pixyfrog/oyster-wind-station/oyster-chassis/renders/antenna.png

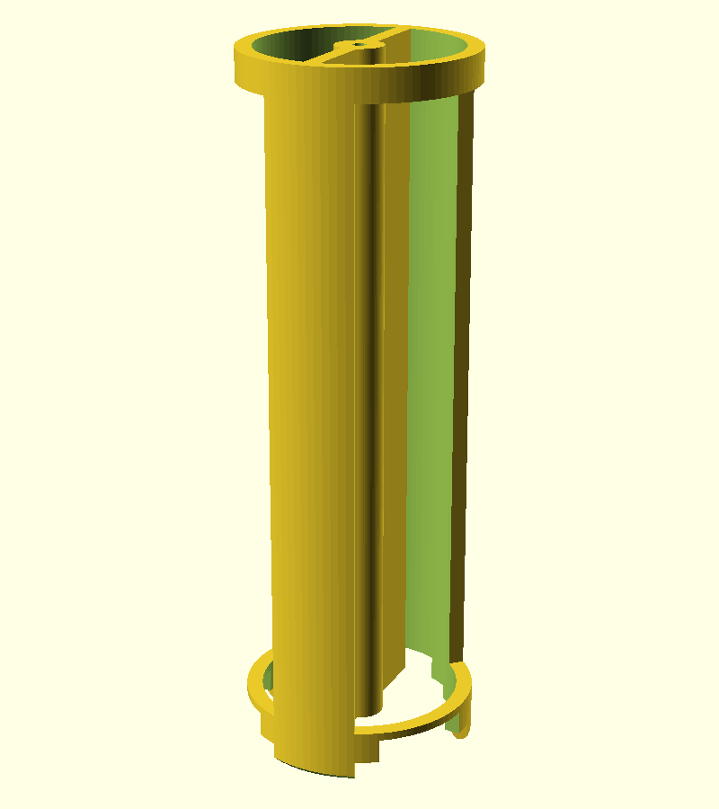
oyster-chassis/renders/antenna.png
