pixyfrog/oyster-wind-station/src/packet.rs

pub fn crc8(data: &[u8]) -> u8 {
    let mut crc: u8 = 0;
    for byte in data {
       crc = crc.wrapping_add(*byte) 
    }
    crc
}

// ---- packet v2 18 bytes ---

pub const MAGIC: u8 = 0xAA;
pub const VERSION_V2: u8 = 0x02;

#[derive(Debug)]
pub struct WindPacketV2 {
    pub node_id: u8,
    pub wind_avg: u16,
    pub wind_gust: u16,
    pub wind_lull: u16,
    pub battery_mv: u16,
    pub sequence: u16,
    pub window_s: u16,
    pub n_sub: u8,
    pub flags: u8,
}

pub fn decode_v2(buf: &[u8]) -> Option<WindPacketV2> {
    if buf.len() != 18 {
        return None;
    }
    if buf[0] != MAGIC {
        return None;
    }
    if buf[1] != VERSION_V2 {
        return None;
    }
    if crc8(&buf[0..17]) != buf[17] {
        return None;
    }
    Some(WindPacketV2 {
        node_id: buf[2],
        wind_avg: ((buf[4] as u16) << 8) | (buf[5] as u16),
        wind_gust: ((buf[6] as u16) << 8) | (buf[7] as u16),
        wind_lull: ((buf[8] as u16) << 8) | (buf[9] as u16),
        battery_mv: ((buf[10] as u16) << 8) | (buf[11] as u16),
        sequence: ((buf[12] as u16) << 8) | (buf[13] as u16),
        window_s: ((buf[14] as u16) << 8) | (buf[15] as u16),
        n_sub: buf[16],
        flags: buf[3],
    })
}
#[cfg(test)]
mod tests {
    use super::*;

    #[test]
    fn reject_v1_length_frame() {
        let mut buf = [0u8; 9];
        buf[0] = MAGIC;
        buf[1] = VERSION_V2;
        assert!(decode_v2(&buf).is_none());
    }

    #[test]
    fn decode_v2_reads_the_fields() {
        let mut buf = [0u8; 18];
        buf[0] = 0xAA;
        buf[1] = 0x02;
        buf[2] = 1;
        buf[3] = 0x05;                   // flags: sensor_ok + window_truncated
        buf[4] = 0x01; buf[5] = 0x90;    // avg   400  = 40.0 m/s
        buf[6] = 0x02; buf[7] = 0x58;    // gust  600
        buf[8] = 0x00; buf[9] = 0x64;    // lull  100
        buf[10] = 0x0E; buf[11] = 0x74;  // batt  3700 mV
        buf[12] = 0x00; buf[13] = 0x2A;  // seq   42
        buf[14] = 0x02; buf[15] = 0x58;  // window_s 600
        buf[16] = 200;                   // n_sub
        buf[17] = crc8(&buf[0..17]);

        let p = decode_v2(&buf).expect("valid v2 packet must decode");
        assert_eq!(p.wind_avg, 400);
        assert_eq!(p.wind_gust, 600);
        assert_eq!(p.wind_lull, 100);
        assert_eq!(p.battery_mv, 3700);
        assert_eq!(p.sequence, 42);
        assert_eq!(p.window_s, 600);
        assert_eq!(p.n_sub, 200);
        assert_eq!(p.flags, 0x05);
}
}
